sweetlilmre/TapuinoNext/include/2-DCube.h

/* C:\Users\petere\Desktop\GTK3VICE-3.5-win64\2-D Cube (19xx)(-).prg (1996/12/24 23:32:00)
   StartOffset(d): 00000000, EndOffset(d): 00002322, Length(d): 00002323 */

const int TestPRGRawDataSize = 2323;

const unsigned char TestPRGRawData[TestPRGRawDataSize] = {
    0x01, 0x08, 0x1B, 0x08, 0x0A, 0x00, 0x8D, 0x20, 0x39, 0x30, 0x30, 0x30, 0x3A, 0x8F, 0x20, 0x49, 0x4E, 0x53, 0x54, 0x52, 0x55, 0x43, 0x54, 0x49, 0x4F, 0x4E, 0x53, 0x00, 0x33, 0x08, 0x14, 0x00,
    0x8D, 0x20, 0x38, 0x30, 0x30, 0x30, 0x3A, 0x8F, 0x20, 0x49, 0x4E, 0x49, 0x54, 0x49, 0x41, 0x4C, 0x49, 0x5A, 0x45, 0x00, 0x4E, 0x08, 0x1E, 0x00, 0x8D, 0x20, 0x37, 0x30, 0x30, 0x30, 0x3A, 0x8F,
    0x20, 0x44, 0x49, 0x53, 0x50, 0x4C, 0x41, 0x59, 0x20, 0x42, 0x4F, 0x41, 0x52, 0x44, 0x00, 0x61, 0x08, 0x28, 0x00, 0x8D, 0x20, 0x36, 0x30, 0x30, 0x30, 0x3A, 0x8F, 0x20, 0x49, 0x4E, 0x50, 0x55,
    0x54, 0x00, 0x72, 0x08, 0x32, 0x00, 0x8B, 0x20, 0x41, 0x24, 0xB2, 0x22, 0x59, 0x22, 0x20, 0xA7, 0x20, 0x8A, 0x00, 0x83, 0x08, 0x3C, 0x00, 0x8B, 0x20, 0x41, 0x24, 0xB2, 0x22, 0x4E, 0x22, 0x20,
    0xA7, 0x20, 0x80, 0x00, 0x8C, 0x08, 0x46, 0x00, 0x89, 0x20, 0x33, 0x30, 0x00, 0x92, 0x08, 0xE7, 0x03, 0x90, 0x00, 0xA8, 0x08, 0x70, 0x17, 0x8F, 0x20, 0x2A, 0x2A, 0x2A, 0x2A, 0x20, 0x49, 0x4E,
    0x50, 0x55, 0x54, 0x20, 0x2A, 0x2A, 0x2A, 0x2A, 0x00, 0xDA, 0x08, 0x7A, 0x17, 0x99, 0x22, 0x13, 0x1C, 0x11, 0x11, 0x11, 0x11, 0x11, 0x11, 0x11, 0x11, 0x11, 0x22, 0x3B, 0xA3, 0x31, 0x36, 0x29,
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
    0x22, 0x59, 0x22, 0x20, 0xAF, 0x20, 0x41, 0x24, 0xB3, 0xB1, 0x22, 0x4E, 0x22, 0x20, 0xA7, 0x20, 0x36, 0x34, 0x31, 0x30, 0x00, 0xFA, 0x0C, 0x28, 0x19, 0x8E, 0x00, 0x18, 0x0D, 0x58, 0x1B, 0x8F,
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
