sweetlilmre/TapuinoNext/include/OLEDFont8x8.h

#include <inttypes.h>

const uint8_t font8x8[] = {
    0x00, 0x00, 0x00, 0x00, 0x00, 0x00, 0x00, 0x00, // [0x20] ' '
    0x00, 0x00, 0x00, 0xDF, 0xDF, 0x00, 0x00, 0x00, // [0x21] '!'
    0x00, 0x03, 0x07, 0x00, 0x03, 0x07, 0x00, 0x00, // [0x22] '"'
    0x00, 0x14, 0x3E, 0x14, 0x3E, 0x14, 0x00, 0x00, // [0x23] '#'
    0x00, 0x24, 0x2A, 0x7F, 0x2A, 0x12, 0x00, 0x00, // [0x24] '$'
    0x43, 0x23, 0x10, 0x08, 0x04, 0x62, 0x61, 0x00, // [0x25] '%'
    0x38, 0x7C, 0x44, 0x7F, 0x3F, 0x04, 0x04, 0x00, // [0x26] '&'
    0x00, 0x00, 0x00, 0x07, 0x07, 0x00, 0x00, 0x00, // [0x27] '''
    0x00, 0x00, 0x7E, 0xFF, 0x81, 0x00, 0x00, 0x00, // [0x28] '('
    0x00, 0x00, 0x81, 0xFF, 0x7E, 0x00, 0x00, 0x00, // [0x29] ')'
    0x08, 0x2A, 0x1C, 0x7F, 0x1C, 0x2A, 0x08, 0x00, // [0x2A] '*'
    0x00, 0x08, 0x08, 0x3E, 0x3E, 0x08, 0x08, 0x00, // [0x2B] '+'
    0x00, 0x00, 0x80, 0xE0, 0x60, 0x00, 0x00, 0x00, // [0x2C] ','
    0x00, 0x08, 0x08, 0x08, 0x08, 0x08, 0x08, 0x00, // [0x2D] '-'
    0x00, 0x00, 0x00, 0xC0, 0xC0, 0x00, 0x00, 0x00, // [0x2E] '.'
    0x00, 0xC0, 0xF0, 0x3C, 0x0F, 0x03, 0x00, 0x00, // [0x2F] '/'
    0x3E, 0x7F, 0x51, 0x49, 0x45, 0x7F, 0x3E, 0x00, // [0x30] '0'
    0x00, 0x40, 0x42, 0x7F, 0x7F, 0x40, 0x40, 0x00, // [0x31] '1'
    0x72, 0x7B, 0x49, 0x49, 0x49, 0x4F, 0x46, 0x00, // [0x32] '2'
    0x22, 0x63, 0x41, 0x49, 0x49, 0x7F, 0x36, 0x00, // [0x33] '3'
    0x07, 0x0F, 0x08, 0x08, 0x08, 0x7E, 0x7E, 0x00, // [0x34] '4'
    0x27, 0x6F, 0x49, 0x49, 0x49, 0x79, 0x31, 0x00, // [0x35] '5'
    0x3E, 0x7F, 0x49, 0x49, 0x49, 0x79, 0x30, 0x00, // [0x36] '6'
    0x01, 0x01, 0x01, 0x01, 0x01, 0x7F, 0x7E, 0x00, // [0x37] '7'
    0x36, 0x7F, 0x49, 0x49, 0x49, 0x7F, 0x36, 0x00, // [0x38] '8'
    0x06, 0x0F, 0x09, 0x09, 0x09, 0x7F, 0x7F, 0x00, // [0x39] '9'
    0x00, 0x00, 0x00, 0x63, 0x63, 0x00, 0x00, 0x00, // [0x3A] ':'
    0x00, 0x00, 0x80, 0xE3, 0x63, 0x00, 0x00, 0x00, // [0x3B] ';'
    0x00, 0x08, 0x1C, 0x36, 0x63, 0x41, 0x00, 0x00, // [0x3C] '<'
    0x00, 0x14, 0x14, 0x14, 0x14, 0x14, 0x14, 0x00, // [0x3D] '='
    0x00, 0x41, 0x63, 0x36, 0x1C, 0x08, 0x00, 0x00, // [0x3E] '>'
    0x02, 0x03, 0xD1, 0xD9, 0x09, 0x0F, 0x06, 0x00, // [0x3F] '?'
    0x3E, 0x7F, 0x41, 0x5D, 0x55, 0x5F, 0x0E, 0x00, // [0x40] '@'
    0x7E, 0x7F, 0x09, 0x09, 0x09, 0x7F, 0x7E, 0x00, // [0x41] 'A'
    0x7F, 0x7F, 0x49, 0x49, 0x49, 0x7F, 0x36, 0x00, // [0x42] 'B'
    0x3E, 0x7F, 0x41, 0x41, 0x41, 0x63, 0x22, 0x00, // [0x43] 'C'
    0x7F, 0x7F, 0x41, 0x41, 0x63, 0x3E, 0x1C, 0x00, // [0x44] 'D'
    0x7F, 0x7F, 0x49, 0x49, 0x49, 0x41, 0x41, 0x00, // [0x45] 'E'
    0x7F, 0x7F, 0x09, 0x09, 0x09, 0x01, 0x01, 0x00, // [0x46] 'F'
    0x3E, 0x7F, 0x41, 0x49, 0x49, 0x7B, 0x7A, 0x00, // [0x47] 'G'
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
};
