sweetlilmre/TapuinoNext/include/Lang.h

#pragma once

namespace TapuinoNext
{
    // init related strings
    const char S_INIT[] = "Init...";
    const char S_INIT_FAILED[] = "Init failed!";
    const char S_INIT_OK[] = "Init OK.";

    // error related strings
    const char S_ERROR[] = "Error:";
    const char S_INVALID_TAP[] = "Invalid TAP!";
    const char S_INVALID_NAME[] = "Invalid Name!";
    const char S_UNKNOWN_TAP[] = "Unknown TAP!";
    const char S_OUT_OF_MEMORY[] = "Out of Memory!";
    const char S_COUNTER_TOO_BIG[] = "Counter too big!";
    const char S_CREATE_FAILED[] = "Create Failed!";
    const char S_COUNTER_GR_SIZE[] = "Count > size!";
    const char S_FILE_ERROR[] = "File Error!";
    const char S_FILE_WRITE_ERROR[] = "File Write Err!";
    const char S_FILE_EXISTS_ERROR[] = "File Exists Err!";
    const char S_CANT_CREATE_DIR[] = "Can't create dir";
    const char S_NO_FILES_FOUND[] = "No Files Found!";
    const char S_FILE_NOT_FOUND[] = "File Not Found!";
    const char S_GR_256_RECORDINGS[] = ">256 Rec files!";
    const char S_RECORDING_FAIL[] = "Recording Fail!";

    // play / rec strings
    const char S_TAP_OK[] = "TAP OK!";
    const char S_LOADING[] = "Loading:";
    const char S_RECORDING[] = "Recording:";
    const char S_SEEKING[] = "Seeking:";
    const char S_SET_COUNTER[] = "Set Counter:";
    const char S_ENTER_FILENAME[] = "Enter Filename:";
    const char S_REC_MODE_MANUAL[] = "Manual";
    const char S_REC_MODE_AUTO[] = "Auto";

    // Menu related strings
    const char S_MAIN_MENU[] = "Main Menu";
    const char S_PLAY_MENU[] = "Play Menu";
    const char S_RECORD_MENU[] = "Record Menu";
    const char S_UPDATE_MENU[] = "Update Menu";
    const char S_SELECT_RECORD_MODE[] = "Name mode:";

    const char S_INSERT_TAP[] = "Insert Tap";
    const char S_RECORD_TAP[] = "Record Tap";
    const char S_PLAY[] = "Play";
    const char S_SEEK[] = "Seek";
    const char S_EXIT[] = "Exit";
    const char S_CONTINUE[] = "Continue";
    const char S_SELECT_TO_START_REC[] = "SELECT to start:";

    const char S_OPTIONS[] = "Options";
    const char S_INPUT_AND_UI[] = "Input & UI";
    const char S_MACHINE[] = "Machine";
    const char S_UPDATE[] = "Update";
    const char S_UPDATE_FW[] = "Update FW";

    // Update related strings
    const char S_UPDATE_UPDATING[] = "FW updating";
    const char S_UPDATE_NOT_FOUND[] = "FW not found!";
    const char S_UPDATE_TOO_SMALL[] = "FW too small!";
    const char S_UPDATE_WRITTEN_OK[] = "FW write OK";
    const char S_UPDATE_UNDERWRITE[] = "FW under write!";
    const char S_UPDATE_WRITTEN[] = "FW written";
    const char S_UPDATE_SUCCESS[] = "Update success!";
    const char S_UPDATE_STARTED[] = "Update started!";
    const char S_UPDATE_REBOOT[] = "Rebooting...!";
    const char S_UPDATE_INCOMPLETE[] = "Upd incomplete!";
    const char S_UPDATE_FAILED[] = "Update failed!";
    const char S_UPDATE_NO_SPACE[] = "No FW space!";

    // Option related strings
    const char S_BTN_CLICK_TIME[] = "Btn Click Time";
    const char S_BTN_HOLD_TIME[] = "Btn Hold Time";
    const char S_TICKER_TIME[] = "Ticker Time";
    const char S_AUTOPLAY[] = "Autoplay";
    const char S_BACKLIGHT[] = "Backlight";
    const char S_MACHINE_TYPE[] = "Machine Type";
    const char S_VIDEO_MODE[] = "Video Mode";
    const char S_ON[] = "on";
    const char S_OFF[] = "off";
    const char S_TRUE[] = "true";
    const char S_FALSE[] = "false";

} // namespace TapuinoNext
