sweetlilmre/TapuinoNext/include/Version.h

    #ifndef FW_BUILD_NUMBER
      #define FW_BUILD_NUMBER "268"
    #endif
    #ifndef FW_VERSION
      #define FW_VERSION "v0.0.3-alpha+268"
    #endif
    #ifndef FW_BUILD_TIME
      #define FW_BUILD_TIME "2022-12-08 11:33:27.510218"
    #endif
    
