sweetlilmre/TapuinoNext/include/ESP32TapeCartLoader.h

#pragma once
#ifdef ESP32

#include <Arduino.h>
#include "UtilityCollection.h"
#include "config.h"

namespace TapuinoNext
{
    class ESP32TapeCartLoader
    {
      public:
        ESP32TapeCartLoader(UtilityCollection* utilityCollection, File& prgFile);
        ~ESP32TapeCartLoader();
        void Init();
        bool CheckForMode();
        bool LoadPRG();

      protected:
        void MotorSignalCallback(bool writeHigh);
        virtual void HWStartSampling();
        virtual void HWStopSampling();

      private:
        bool FastSendByte(uint8_t byte);
        UtilityCollection* utilityCollection;
        FlipBuffer* flipBuffer;
        static ESP32TapeCartLoader* internalClass;
        static void IRAM_ATTR MotorSignalCallbackStatic();
        volatile uint16_t shiftReg;
        bool loaderMode;
        File prgFile;
        uint16_t callAddr, loadAddr, endAddr;
    };
} // namespace TapuinoNext
#endif
