sweetlilmre/TapuinoNext/include/Options.h

#pragma once
#include <inttypes.h>
#include "FileLoader.h"
#include "MenuTypes.h"
#include "OptionTypes.h"
#include "InputHandler.h"
#include "Menu.h"

namespace TapuinoNext
{
    class Options
    {
      public:
        Options(FileLoader* fileLoader, IChangeNotify* notify, MenuHandler* menuHandler, ActionCallback* updateCallback);
        void LoadOptions();
        void SaveOptions();
        void OnAction();

        ValueOption btnClickTime;
        ValueOption btnHoldTime;
        ValueOption tickerTime;
        ValueOption tickerHoldTime;
        ToggleOption ntscPAL;
        ToggleOption autoPlay;
        ToggleOption backlight;
        EnumOption machineType;

      protected:
        const char* TagIdToString(OptionTagId id);
        FileLoader* fileLoader;
        MenuHandler* menuHandler;
        std::vector<IOptionType*> allOptions;
    };
} // namespace TapuinoNext
